Prokuon/term512/assets/20260914220759.jpg

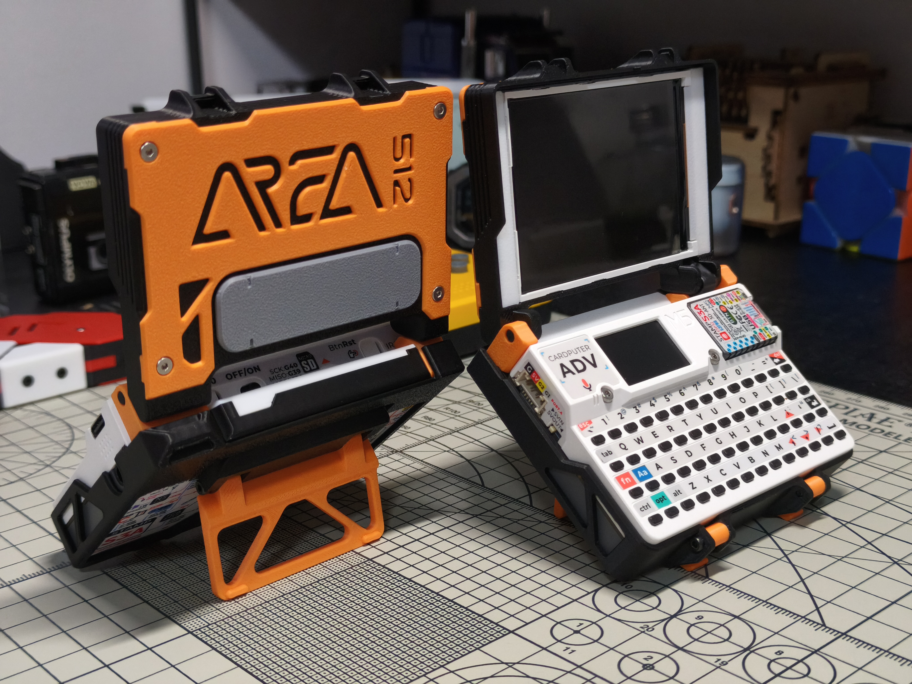
assets/20260914220759.jpg
