Prokuon/term512/assets/20260919124935.jpg

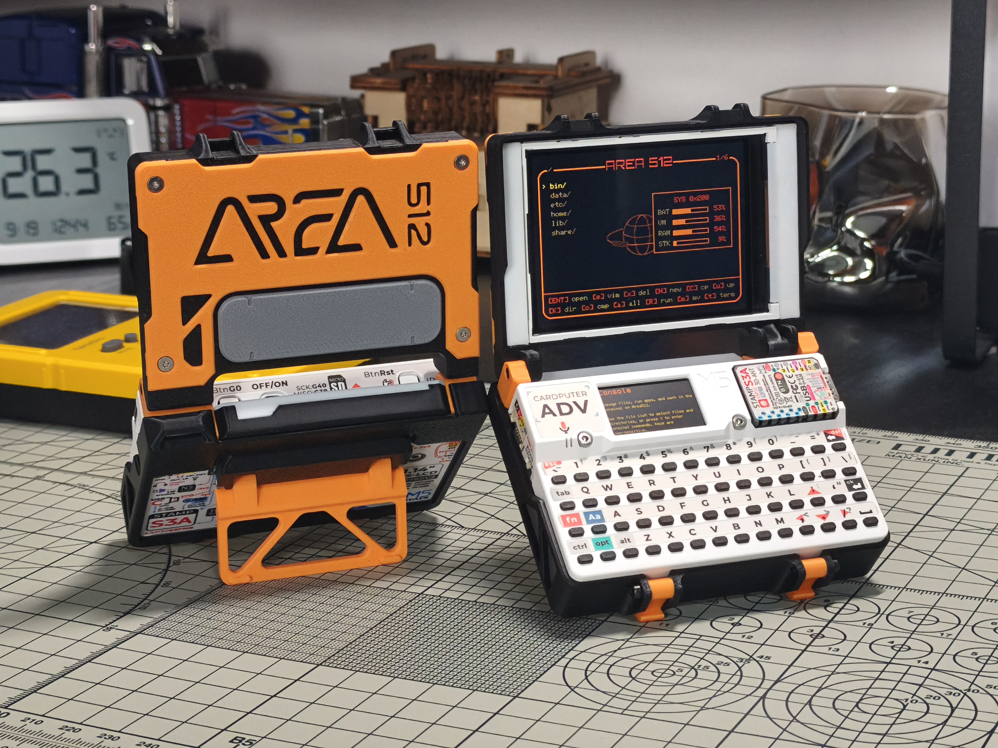
assets/20260919124935.jpg
