Prokuon/term512/Model/TypeB/STL/CaseC2.stl

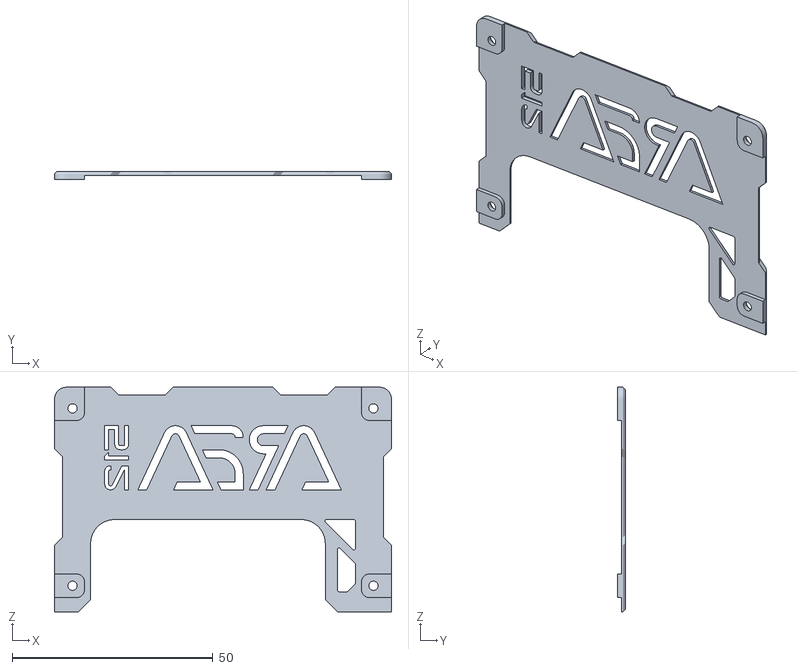
[picture p38: CAD file, 2026-09-15]
Model/TypeB/STL/CaseC2.stl
84.0 x 2.00 x 56.0
