Prokuon/term512/Model/TypeB/STL/CaseS1.stl

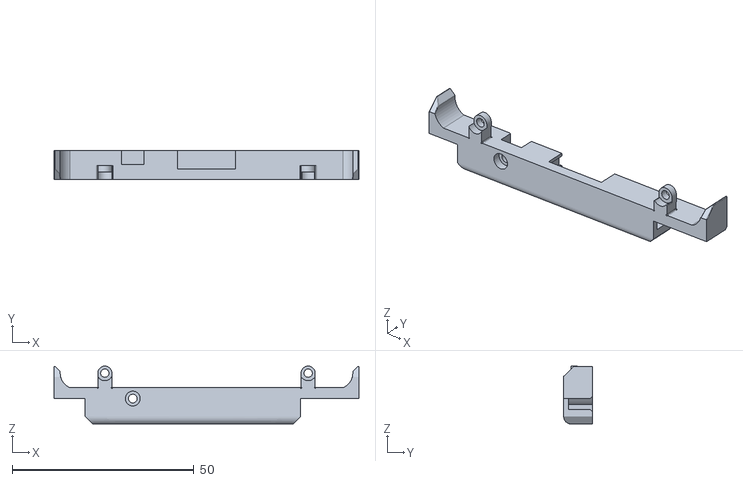
[picture p39: CAD file, 2026-09-15]
Model/TypeB/STL/CaseS1.stl
84.0 x 7.90 x 16.0
