Prokuon/term512/Model/TypeA/STL/CaseT1.stl

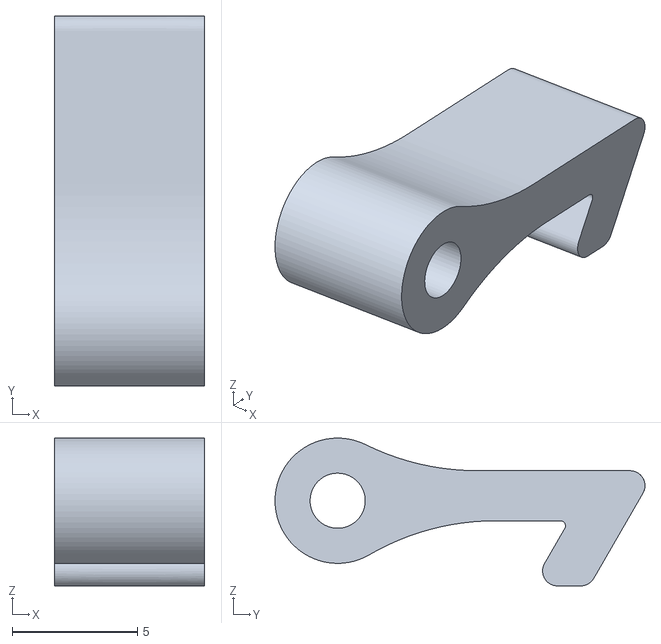
[picture p40: CAD file, 2026-09-15]
Model/TypeA/STL/CaseT1.stl
6.00 x 14.8 x 5.90
