Prokuon/term512/Model/TypeB/STL/CaseD3.stl

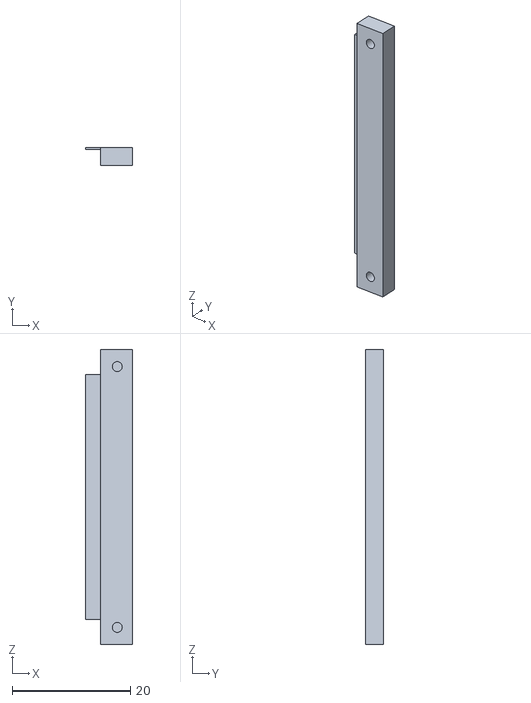
[picture p41: CAD file, 2026-09-15]
Model/TypeB/STL/CaseD3.stl
8.00 x 3.10 x 50.0
